Anuki16/package-delivery-safe-box/pcb/3d models/B8B-XH-A-LF--SN---3DModel-STEP-418109.STEP

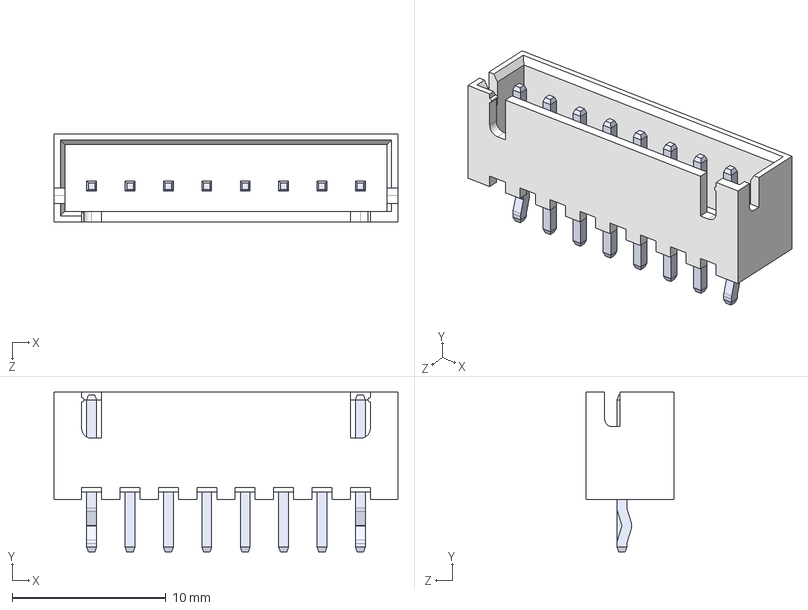
[picture p16: CAD file, 2023-08-14]
pcb/3d models/B8B-XH-A-LF--SN---3DModel-STEP-418109.STEP
22.4 x 10.4 x 5.75 mm
