Anuki16/package-delivery-safe-box/enclosure/pcb3d.step.SLDPRT

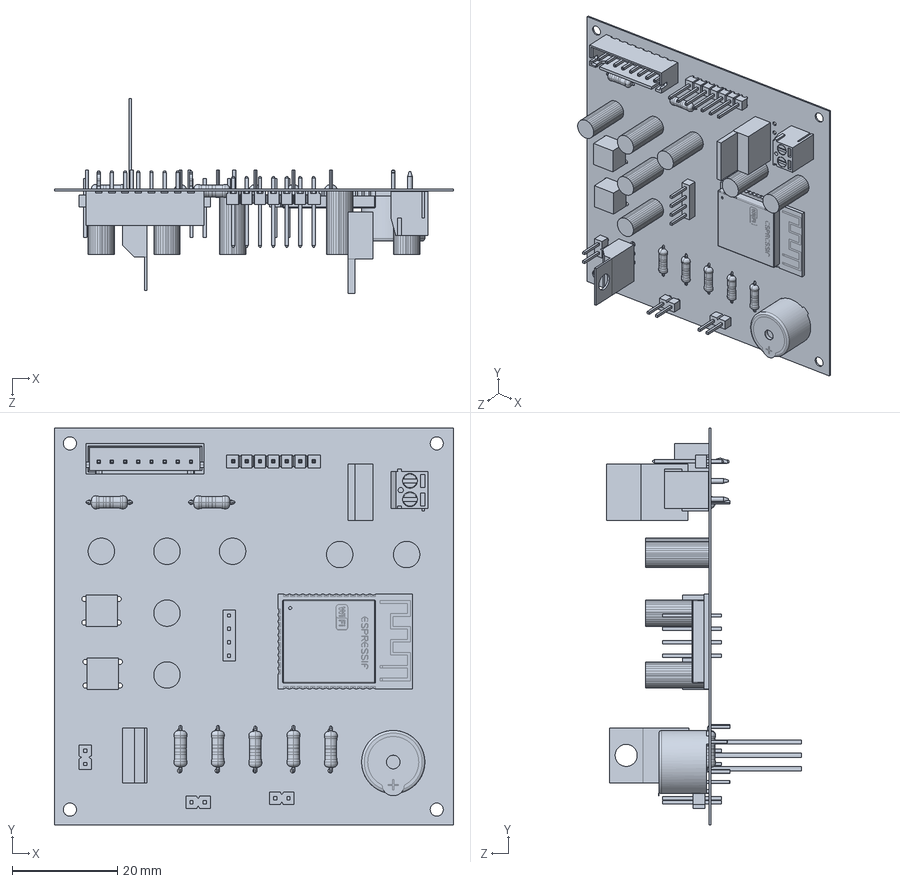
[picture p17: CAD file, 2023-08-14]
enclosure/pcb3d.step.SLDPRT
75.7 x 75.3 x 36.9 mm
