Anuki16/package-delivery-safe-box/pcb/3d models/5-103327-1--3DModel-STEP-1.STEP

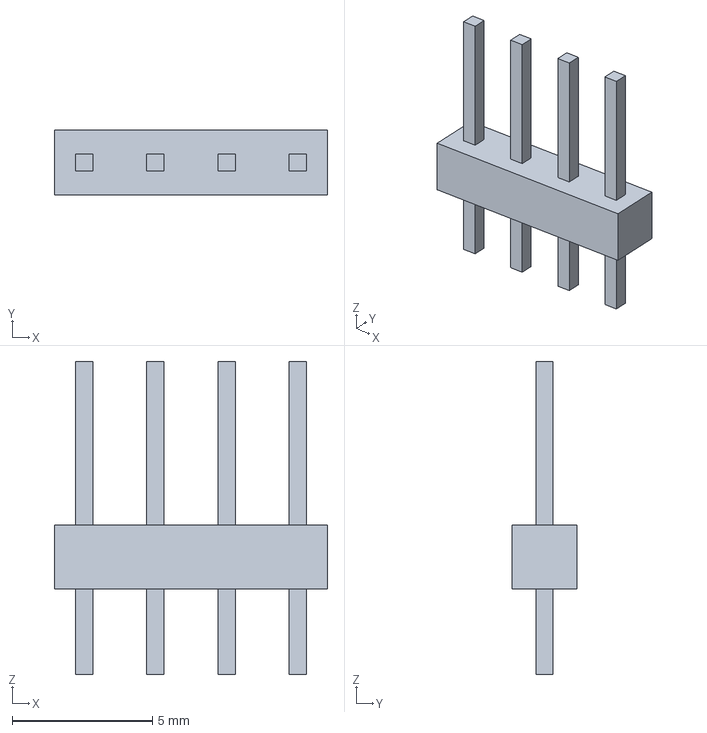
[picture p18: CAD file, 2023-08-14]
pcb/3d models/5-103327-1--3DModel-STEP-1.STEP
9.75 x 2.34 x 11.2 mm
