Anuki16/package-delivery-safe-box/pcb/3d models/resistor025W-10k.STEP

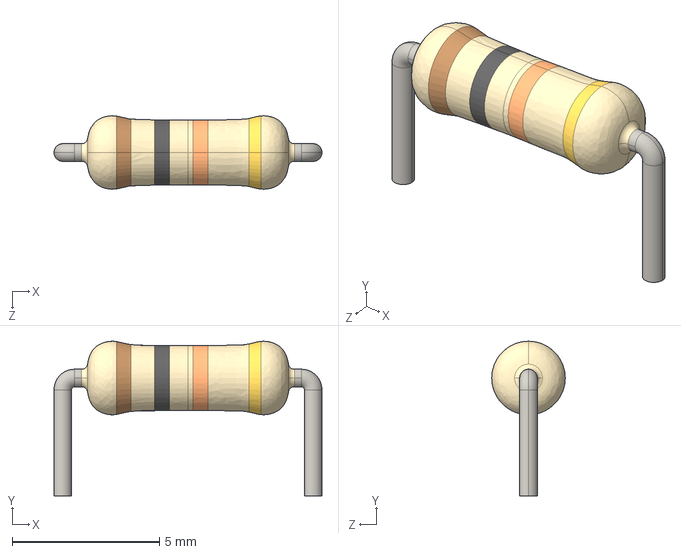
[picture p19: CAD file, 2023-08-14]
pcb/3d models/resistor025W-10k.STEP
9.10 x 5.25 x 2.50 mm
