Anuki16/package-delivery-safe-box/enclosure/lock_button_mount.SLDPRT

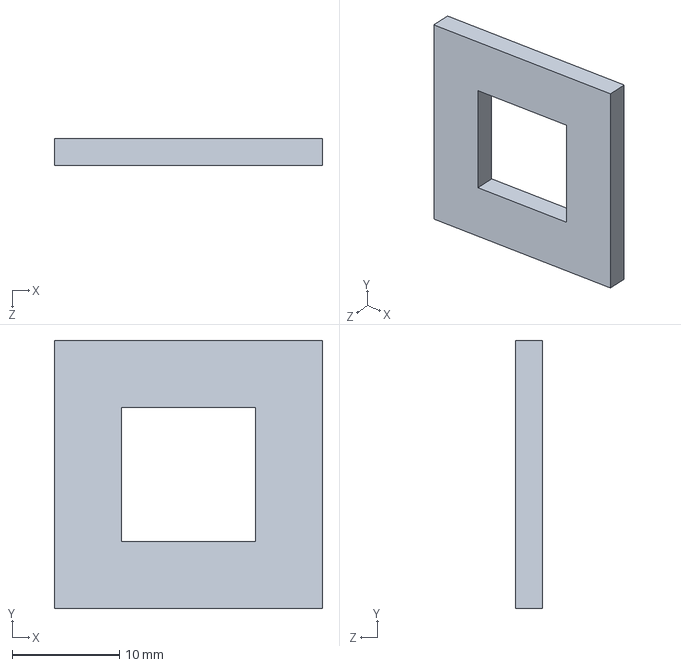
[picture p20: CAD file, 2023-08-14]
enclosure/lock_button_mount.SLDPRT
25.0 x 25.0 x 2.50 mm
