Anuki16/package-delivery-safe-box/enclosure/led_panel_laser.SLDPRT

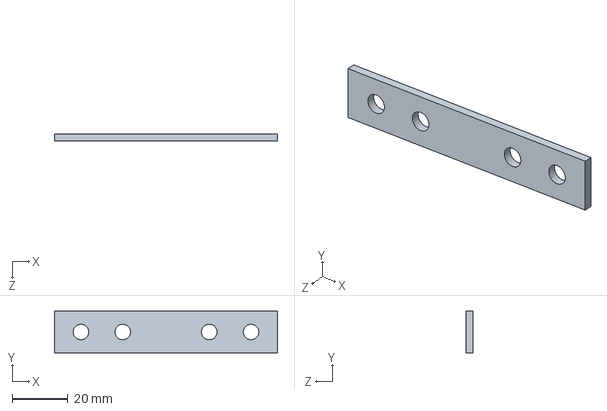
[picture p21: CAD file, 2023-08-14]
enclosure/led_panel_laser.SLDPRT
80.0 x 15.0 x 2.50 mm
