Anuki16/package-delivery-safe-box/enclosure/3 Battery Holder With Batteries.step.SLDPRT

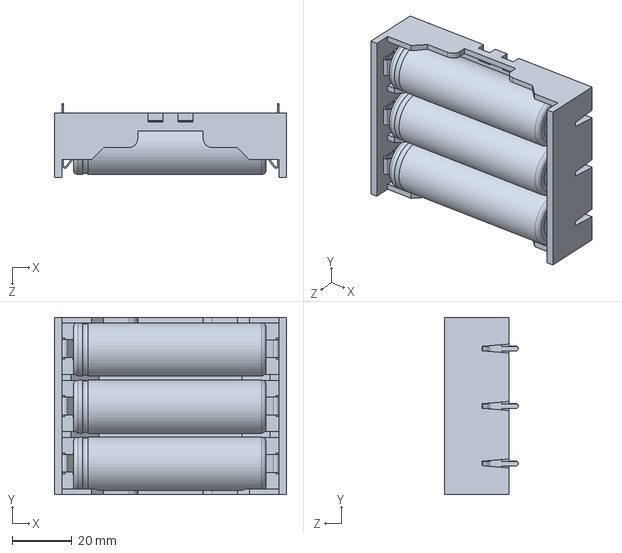
[picture p23: CAD file, 2023-08-14]
enclosure/3 Battery Holder With Batteries.step.SLDPRT
78.0 x 59.6 x 24.7 mm
