Anuki16/package-delivery-safe-box/enclosure/enclosure_box_molding.SLDPRT

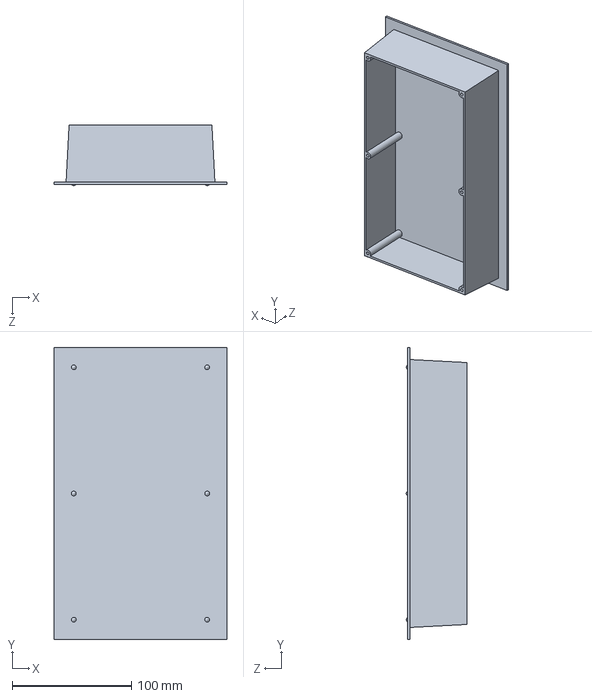
[picture p24: CAD file, 2023-08-14]
enclosure/enclosure_box_molding.SLDPRT
145.2 x 245.2 x 51.2 mm
