Anuki16/package-delivery-safe-box/enclosure/door.SLDPRT

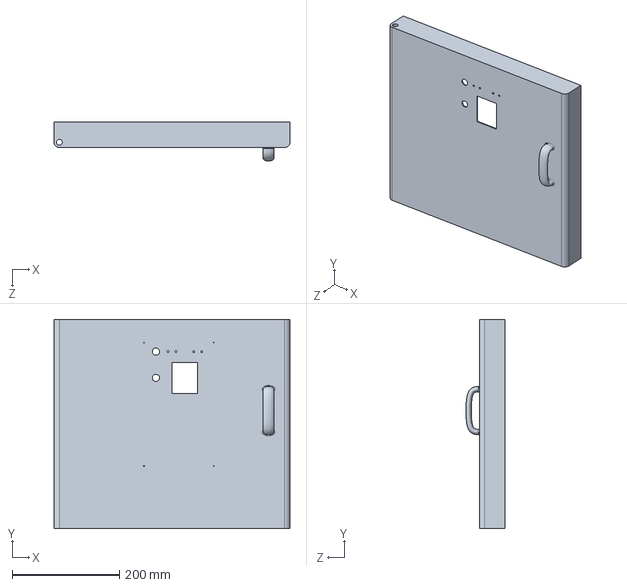
[picture p25: CAD file, 2023-08-14]
enclosure/door.SLDPRT
440.0 x 390.0 x 73.0 mm
