Anuki16/package-delivery-safe-box/enclosure/door_new.SLDPRT

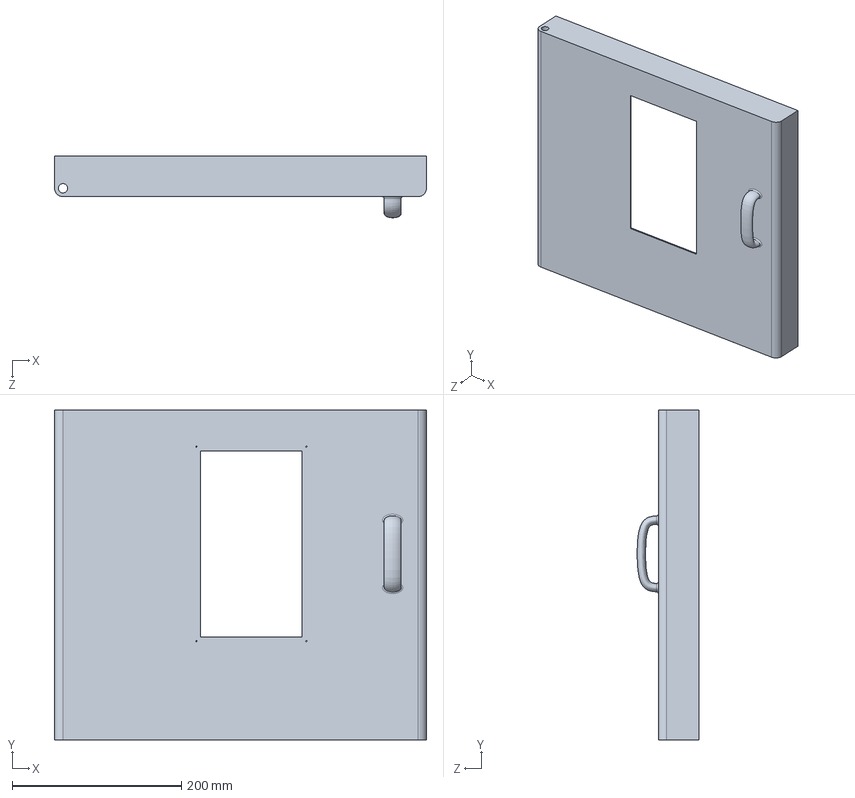
[picture p26: CAD file, 2023-08-14]
enclosure/door_new.SLDPRT
440.0 x 390.0 x 73.0 mm
