Anuki16/package-delivery-safe-box/enclosure/battery_holder_casing.SLDPRT

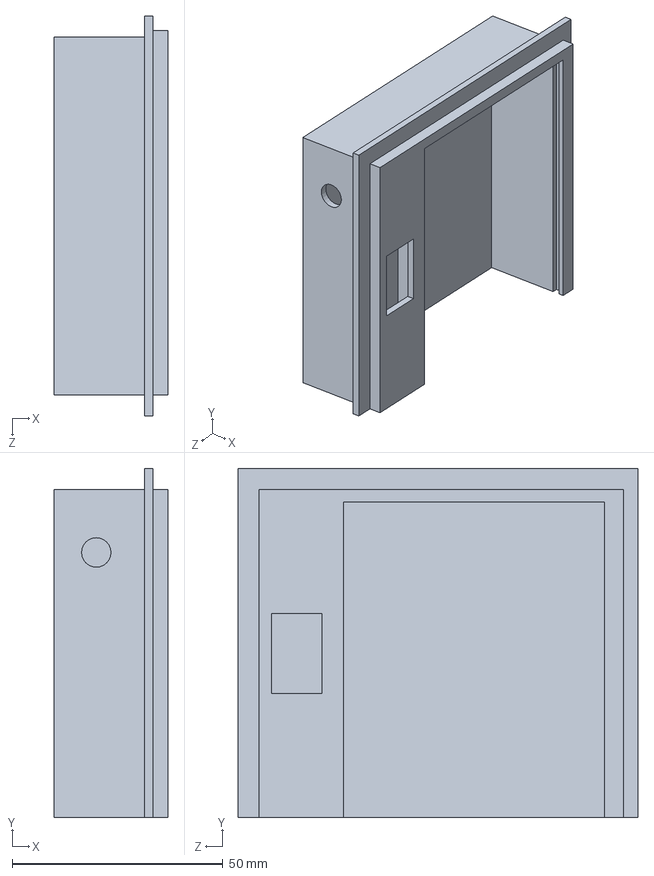
[picture p27: CAD file, 2023-08-14]
enclosure/battery_holder_casing.SLDPRT
27.0 x 83.0 x 95.0 mm
