Anuki16/package-delivery-safe-box/enclosure/lock_slot_laser.SLDPRT

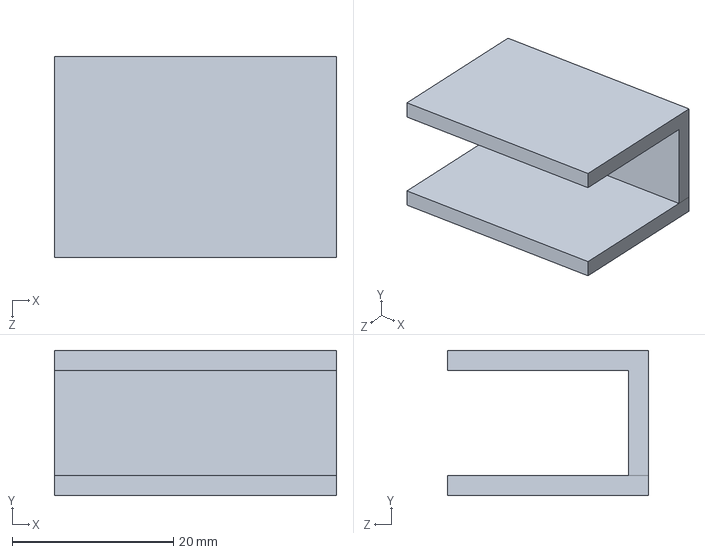
[picture p28: CAD file, 2023-08-14]
enclosure/lock_slot_laser.SLDPRT
35.0 x 18.0 x 25.0 mm
