Anuki16/package-delivery-safe-box/enclosure/lock_short_side.SLDPRT

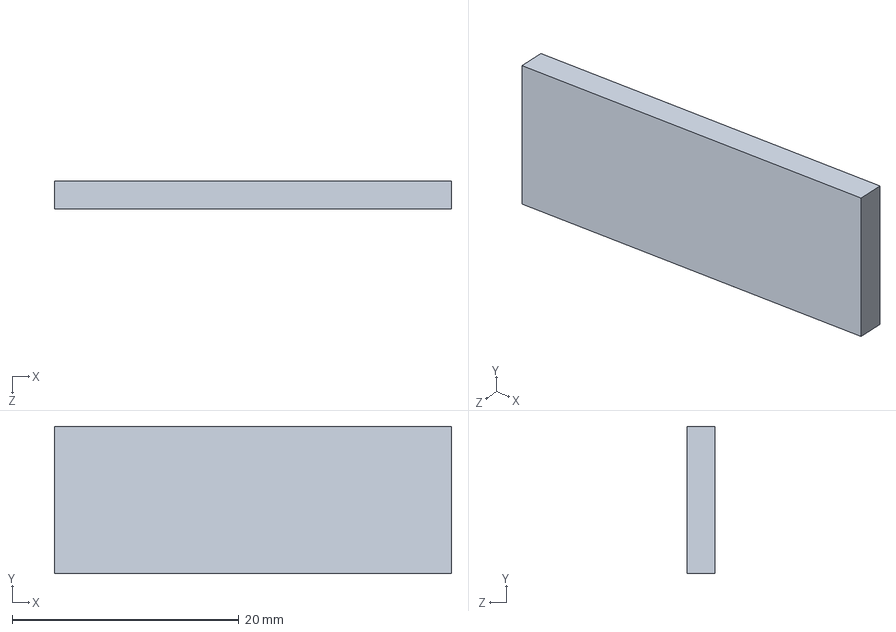
[picture p29: CAD file, 2023-08-14]
enclosure/lock_short_side.SLDPRT
35.0 x 13.0 x 2.50 mm
