Anuki16/package-delivery-safe-box/enclosure/lock_long_side.SLDPRT

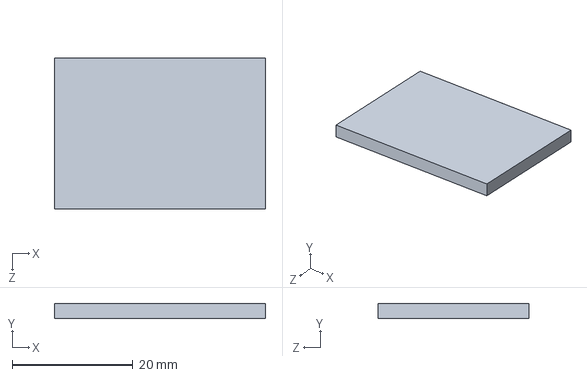
[picture p30: CAD file, 2023-08-14]
enclosure/lock_long_side.SLDPRT
35.0 x 2.50 x 25.0 mm
