Anuki16/package-delivery-safe-box/enclosure/box.SLDPRT

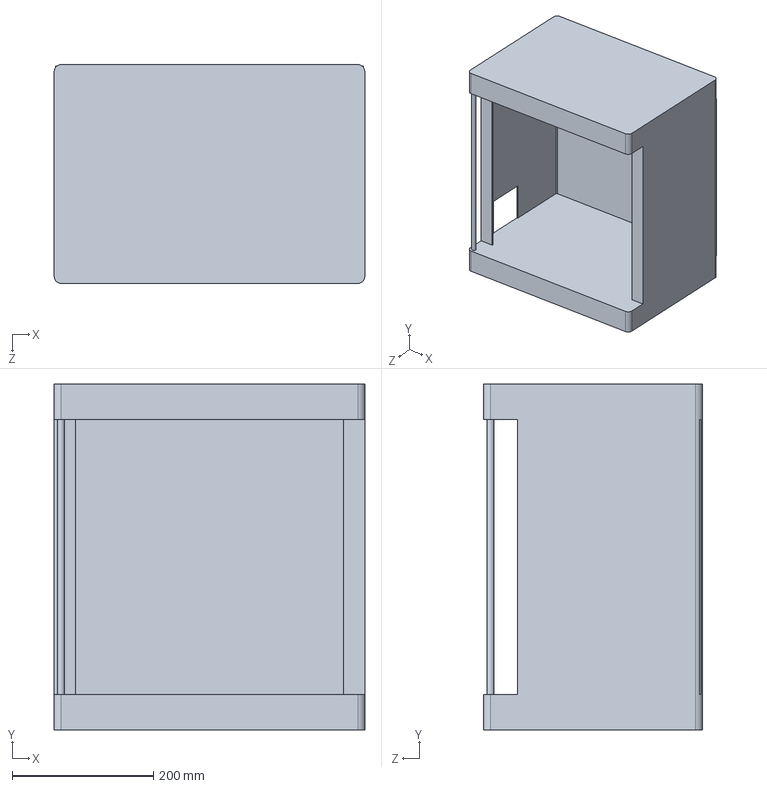
[picture p31: CAD file, 2023-08-14]
enclosure/box.SLDPRT
440.0 x 490.0 x 310.0 mm
