Anuki16/package-delivery-safe-box/enclosure/lock_buzzer_mount.SLDPRT

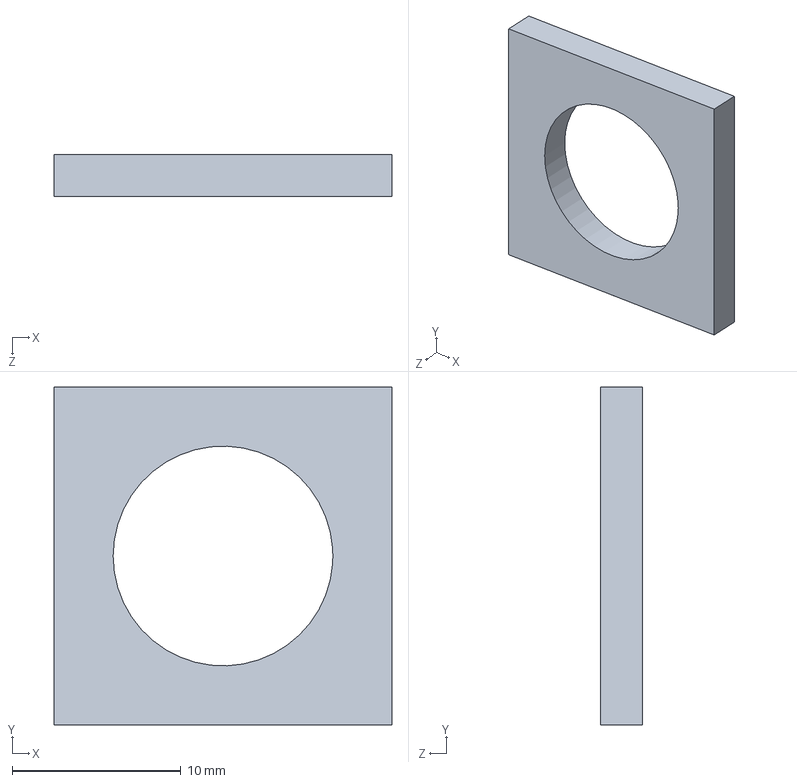
[picture p32: CAD file, 2023-08-14]
enclosure/lock_buzzer_mount.SLDPRT
20.0 x 20.0 x 2.50 mm
