Anuki16/package-delivery-safe-box/enclosure/led_panel.SLDPRT

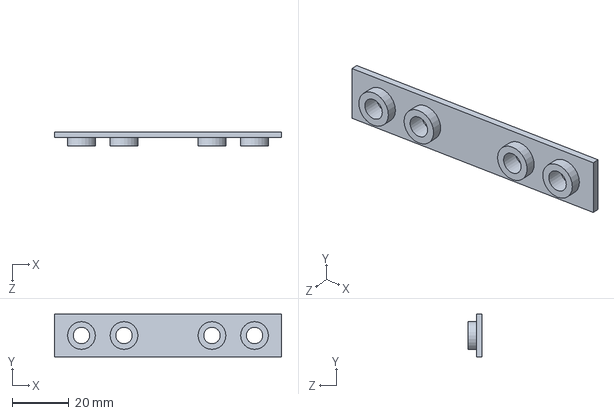
[picture p33: CAD file, 2023-08-14]
enclosure/led_panel.SLDPRT
80.0 x 15.0 x 5.00 mm
