Anuki16/package-delivery-safe-box/enclosure/lock_slot.SLDPRT

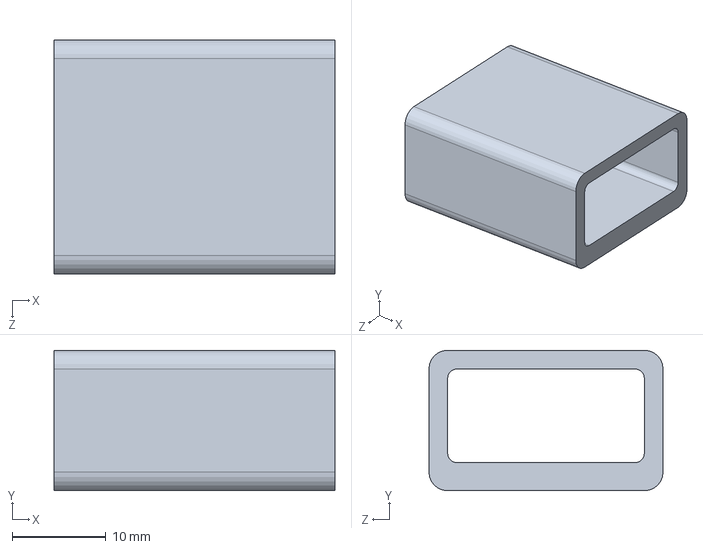
[picture p34: CAD file, 2023-08-14]
enclosure/lock_slot.SLDPRT
30.0 x 15.0 x 25.0 mm
